solene-drnx/Luciole-Public/Application/assets/bus.png

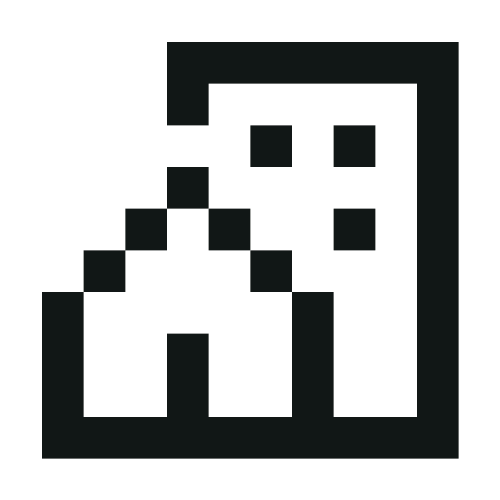
Application/assets/bus.png
