solene-drnx/Luciole-Public/Application/assets/clock.png

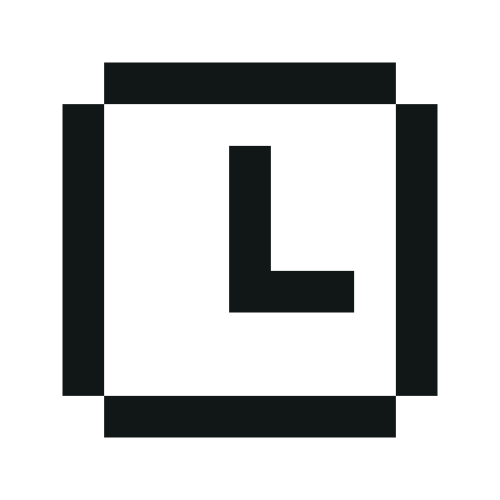
Application/assets/clock.png
