solene-drnx/Luciole-Public/Application/assets/greyScript_text.png

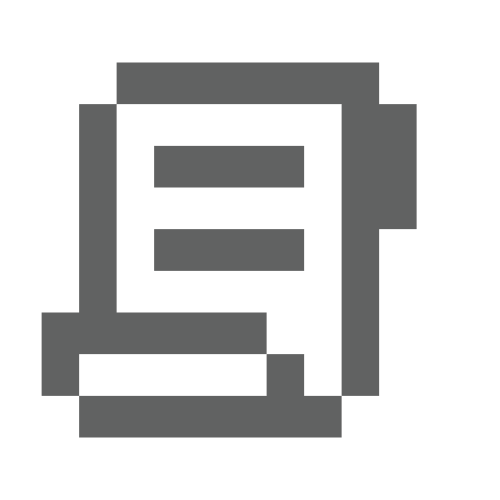
Application/assets/greyScript_text.png
