solene-drnx/Luciole-Public/Application/assets/moon.png

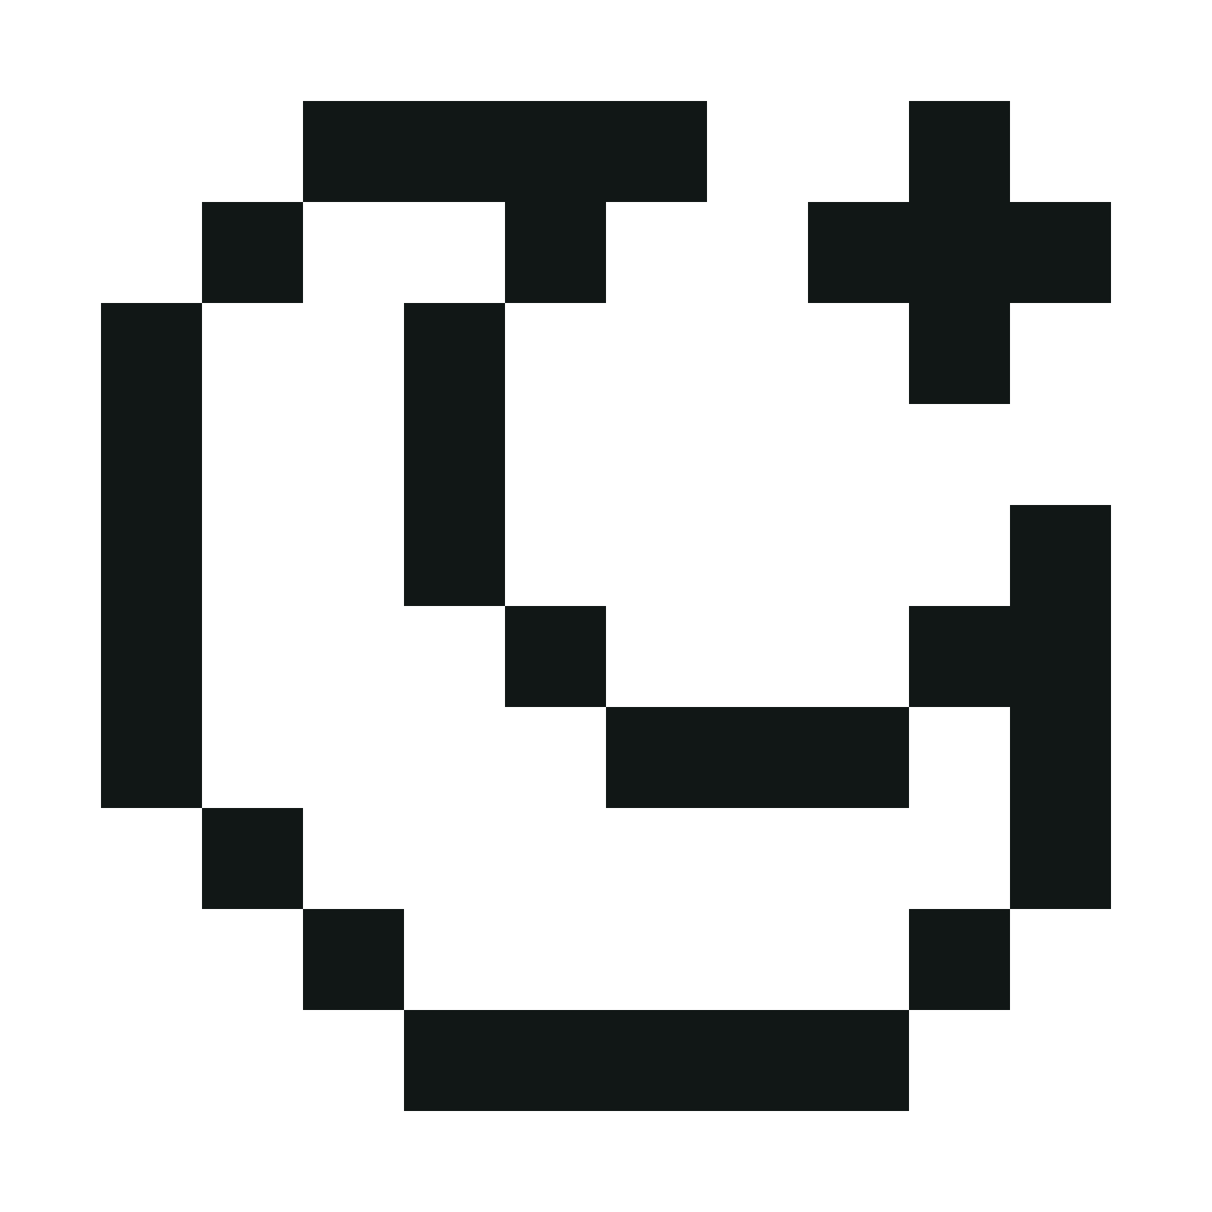
Application/assets/moon.png
