solene-drnx/Luciole-Public/Application/assets/radio.png

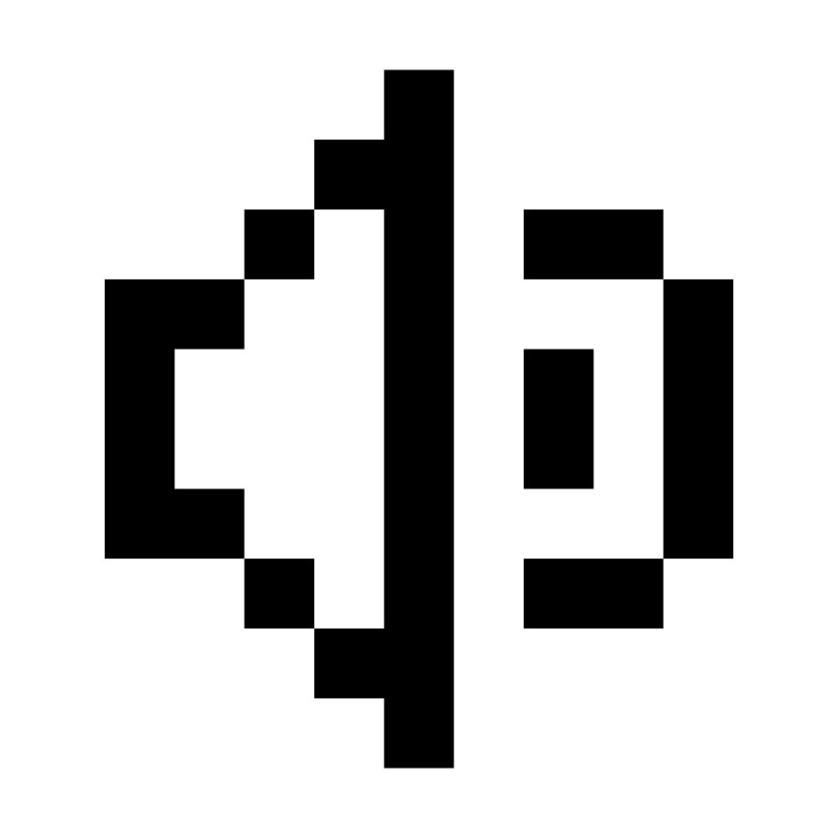
Application/assets/radio.png
